softip/monitoramento_solar/solarmon/assets/uploads/plantas/52ae2-sistema-fotovoltaico-artigos-cursos-cpt.jpg

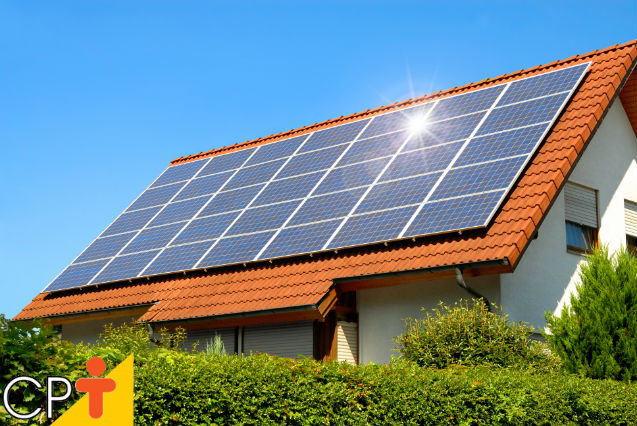
solarmon/assets/uploads/plantas/52ae2-sistema-fotovoltaico-artigos-cursos-cpt.jpg
