softip/monitoramento_solar/circuito.jpg

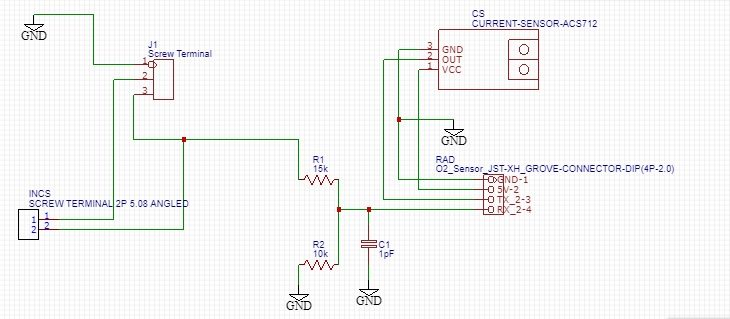
circuito.jpg
