softip/monitoramento_solar/fotos/09052019_1.jpg

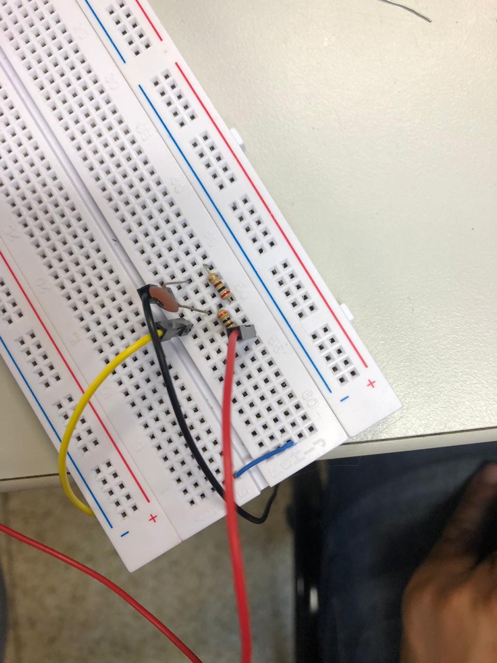
fotos/09052019_1.jpg
