softip/monitoramento_solar/fotos/09052019_2.jpg

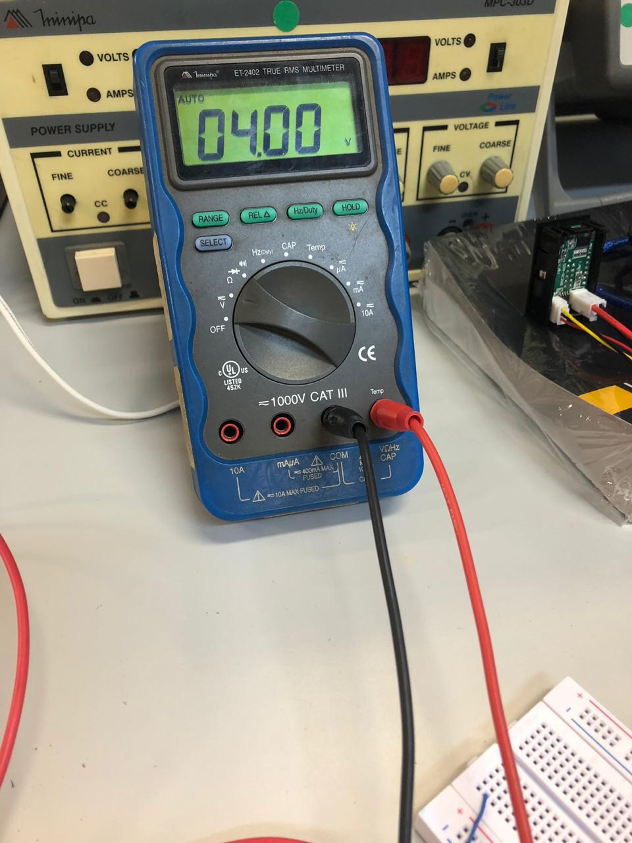
fotos/09052019_2.jpg
