softip/monitoramento_solar/fotos/09052019_3.jpg

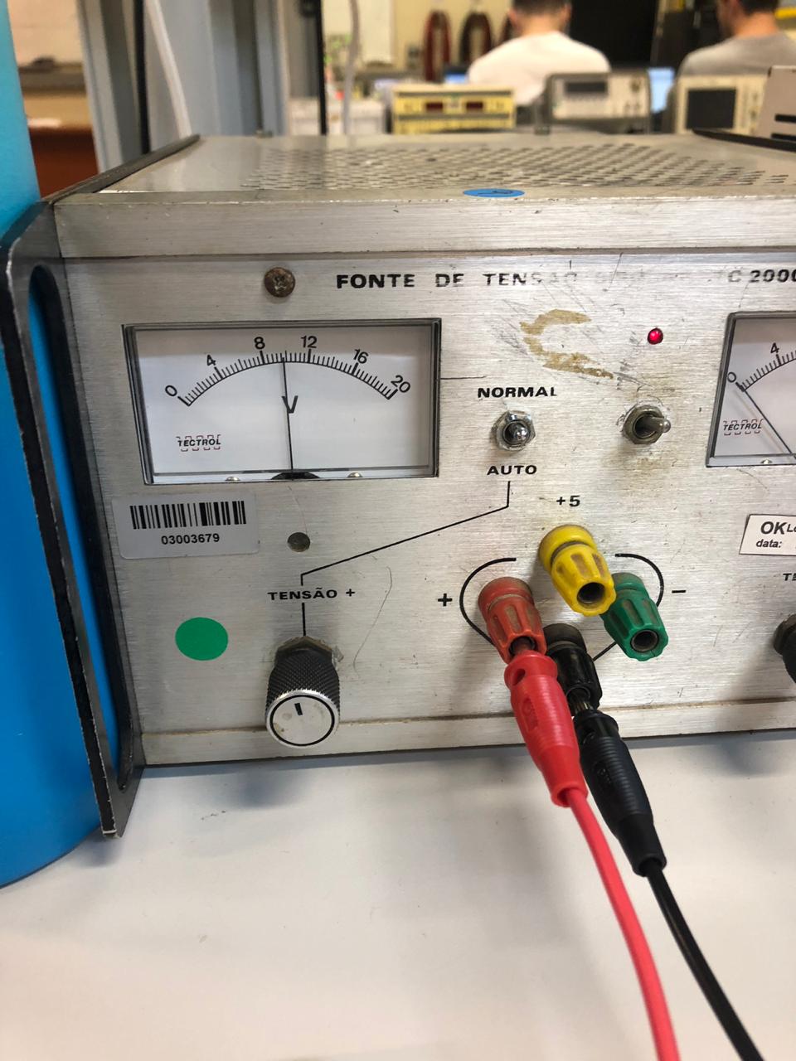
fotos/09052019_3.jpg
