softip/monitoramento_solar/fotos/09052019_4.jpg

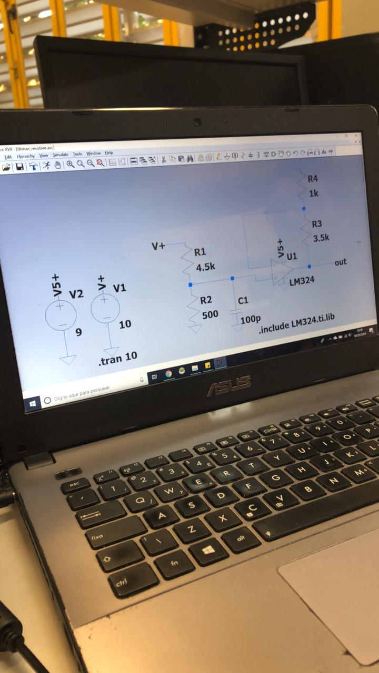
fotos/09052019_4.jpg
