softip/monitoramento_solar/fotos/09052019_5.jpg

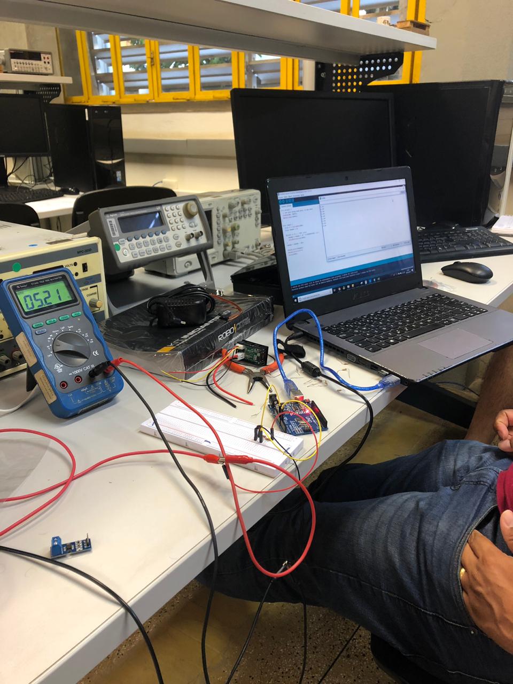
fotos/09052019_5.jpg
