softip/monitoramento_solar/fotos/09052019_6.jpg

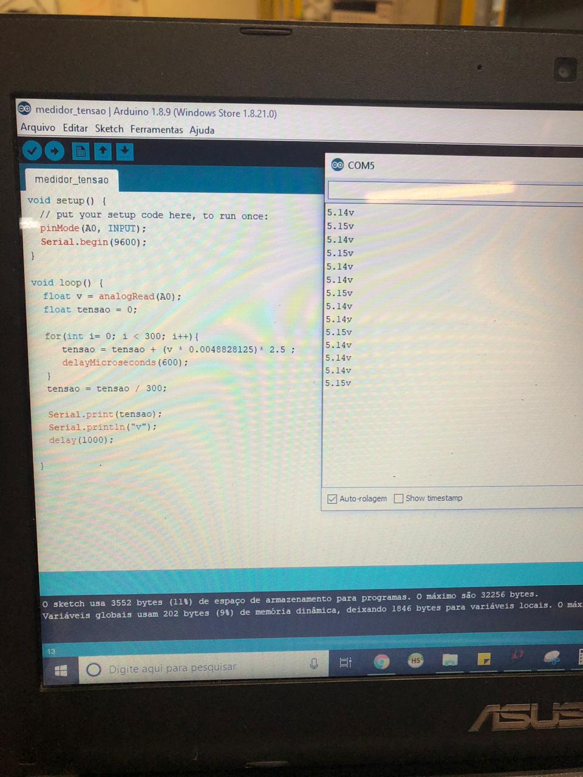
fotos/09052019_6.jpg
