softip/monitoramento_solar/fotos/25042919.jpg

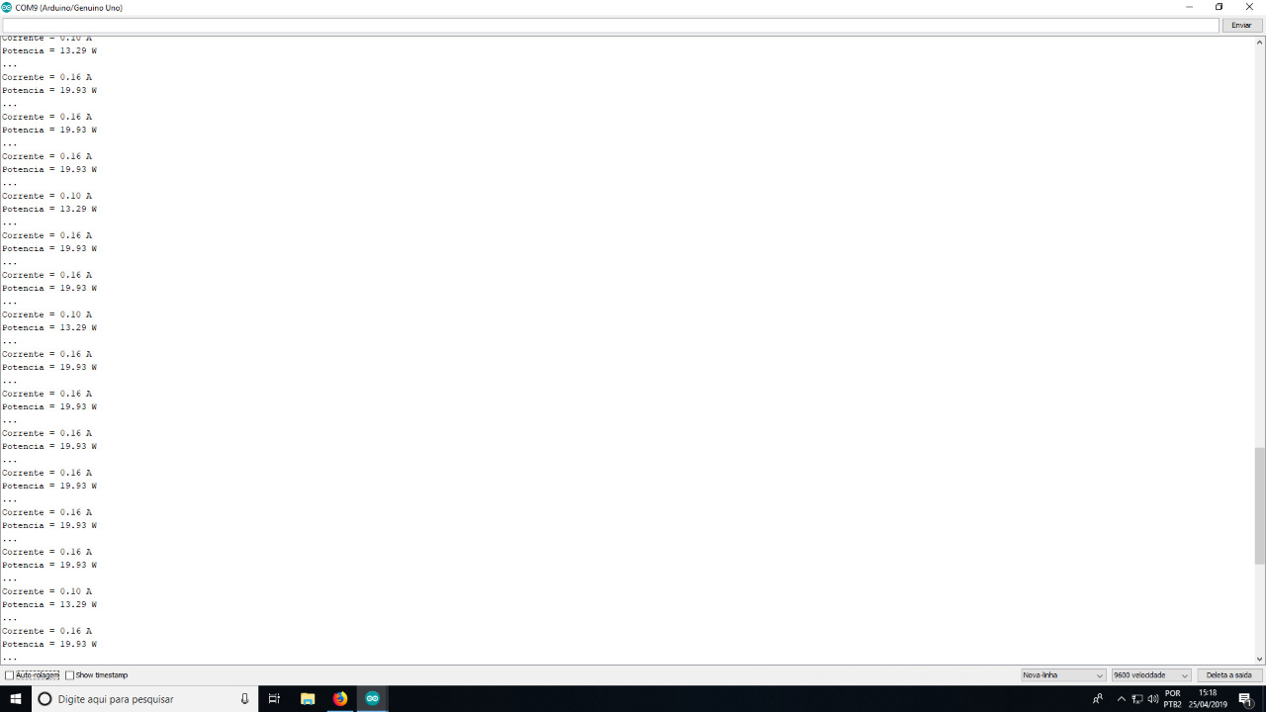
fotos/25042919.jpg
