softip/monitoramento_solar/fotos/divisor_resistivo.jpg

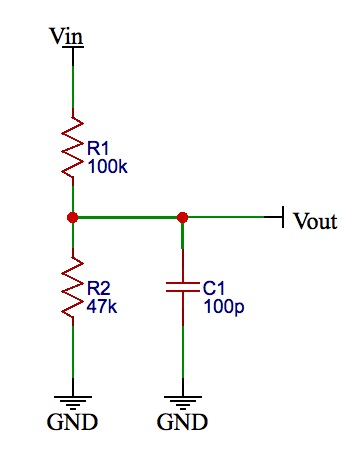
fotos/divisor_resistivo.jpg
