softip/monitoramento_solar/solarmon/assets/uploads/clientes/2666a-unicamp.png

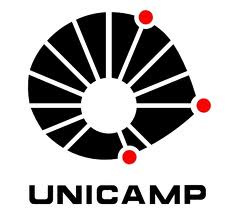
solarmon/assets/uploads/clientes/2666a-unicamp.png
