softip/monitoramento_solar/solarmon/assets/uploads/plantas/c3c21-untitled-1.jpg

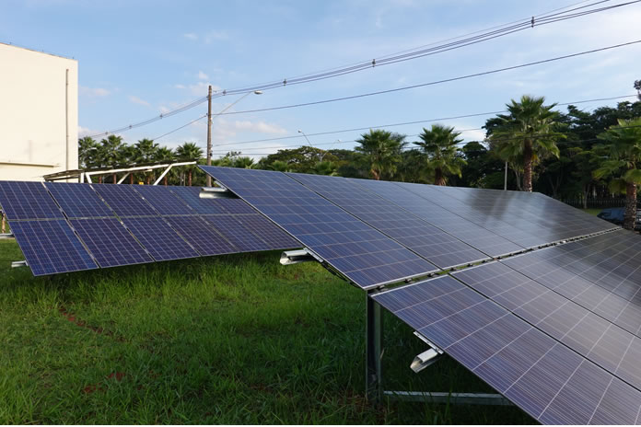
solarmon/assets/uploads/plantas/c3c21-untitled-1.jpg
