softip/monitoramento_solar/Sensor/Headers.h

// Header.h : cabecalhos de classes

// Mais informacoes em www.radiuino.cc
// Copyright (c) 2015
// Author: Pedro Henrique Gomes, Omar C. Branquinho, Tiago T. Ganselli e Debora M Ferreira, Guilherme Lopes da Silva, Raphael Montali de Assumpçao.
// Versao 2.3: 18/05/2017

// Este arquivo e parte da plataforma Radiuino
// Este programa e um software livre; voce pode redistribui-lo e/ou modifica-lo dentro dos termos da Licenca Publica Geral Menor GNU 
// como publicada pela Fundacao do Software Livre (FSF); na versao 2 da Licenca, ou (na sua opniao) qualquer futura versao.
// Este programa e distribuido na esperanca que possa ser  util, mas SEM NENHUMA GARANTIA; sem uma garantia implicita 
// de ADEQUACAO a qualquer MERCADO ou APLICACAO EM PARTICULAR. Veja a Licenca Publica Geral Menor GNU para maiores detalhes.
// Voce deve ter recebido uma copia da Licenca Publica Geral Menor GNU junto com este programa, se nao, escreva para a Fundacao 
// do Software Livre(FSF) Inc., 51 Franklin St, Fifth Floor, Boston, MA  02110-1301  USA
    
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
#ifndef HEADERS_H
#define HEADERS_H 1

/**
 * Estrutura do pacote a ser transmitido e recebido. O pacote possui 52 bytes, sendo 4 bytes de cabecalho de camada fisica (Phy), 4 bytes de cabecalho
 * de camada de Controle de Acesso ao Meio (MAC), 4 bytes de cabecalho de camada de Rede (Net), 4 bytes de cabecalho de camada de Transporte (Transp) e
 * e 4 bytes de cabecalho de camada de Aplicacao (App). Os 36 bytes restantes sao reservados para payload de AD e IO.
 */
typedef struct 
{  
  /* Cabecalho da camada Fisica (Phy) */
  byte PhyHdr[4];
  
  /* Cabecalho da camada de Controle de Acesso ao Meio (MAC) */
  byte MACHdr[4];
  
  /* Cabecalho da camada de Rede (Net) */
  byte NetHdr[4];
  
  /* Cabecalho da camada de Transporte (Transp) */
  byte TranspHdr[4];
  
  
  
  /* Bytes o payload de AD */
  byte AD0[3];
  byte AD1[3];
  byte AD2[3];
  byte AD3[3];
  byte AD4[3];
  byte AD5[3];  
  
  /* Bytes do payload de IO */
  byte IO0[3];
  byte IO1[3];
  byte IO2[3];
  byte IO3[3];
  byte IO4[3];
  byte IO5[3];  
  
} packet;

packet g_pkt;

/**
 * Classe de camada de Aplicacao
 */
 
#define AD0_PIN  0
#define AD1_PIN  1
#define AD2_PIN  2
#define AD3_PIN  3
#define AD4_PIN  4
#define AD5_PIN  5

#define IO0_PIN  4
#define IO1_PIN  5
#define IO2_PIN  6
#define IO3_PIN  7
#define IO4_PIN  8
#define IO5_PIN  9

class APP
{
  public:
    APP(void);
    inline void initialize(void);
    inline void send(packet * pkt);
    inline void receive(packet * pkt);

  private:
    int IO_0, IO_1, IO_2, IO_3, IO_4, IO_5;

};

/* Objeto de acesso a classe da camada de Aplicacao */
extern APP App;

/**
 * Classe de camada de Transporte
 */
class TRANSP
{
  public:
    TRANSP(void);
    inline void initialize(void);
    inline void send(packet * pkt);
    inline void receive(packet * pkt);

  private:
  
};

/* Objeto de acesso a classe da camada de Transporte */
extern TRANSP Transp;

/**
 * Classe de camada de Rede
 */
class NET
{
  public:
    NET(void);
    inline void initialize(void);
    inline void send(packet * pkt);
    inline void receive(packet * pkt);
    void swapAddresses(packet * pkt);
    
    byte my_addr;
  private:
    
};

/* Objeto de acesso a classe da camada de Rede */
extern NET Net;

/**
 * Classe de camada de Controle de Acesso ao Meio
 */
#define  SLEEP_MSG  1
#define  SLEEP_ACK  2
#define  SLEEP2_MSG  3
#define  SLEEP2_ACK  4

class MAC
{
  public:
    MAC(void);
    inline void initialize(void);
    inline void send(packet * pkt);
    inline void receive(packet * pkt);
    
    volatile int time_to_sleep;
    /* variaveis para o sleep2 */
    volatile unsigned long t2;
    volatile int t3;
    volatile boolean flag_sleep2;
    volatile unsigned long last_wakeup;
  private:
    
};

/* Objeto de acesso a classe da camada de Controle de Acesso ao Meio */
extern MAC Mac;

/**
 * Classe de camada Fisica
 */
#define BUFFLEN1  CC1101_PACKT_LEN
byte serialData[BUFFLEN1 + 1];

class PHY
{
  public:
    PHY(void);
    inline void initialize();
    inline void send(packet * pkt);
    inline int receive(packet * pkt);
    
    void sendSerial(packet * pkt);
    void receiveSerial(void);
    
    byte txFifoFree(void);
    void setChannel(byte channel);
    void lowPowerOn(void);    
    void setPower(byte power);
    void setFreqOffset(byte freq_offset);
    void setRadio(int set_radio);
    
    boolean carrierSense(void);
    
    byte power;                 /* Potencia */
    byte channel;               /* Canal */
    byte freq_offset;           /* Offset de frequencia */
    int serial_baudrate;        /* Serial baudrate */
    int set_radio;        /* Ajusta o tipo de rádio */
    
    //incremento do pisca do led
    int RxLedBlink;
    int TxLedBlink;
  
  private:
    int initCC1101Config(void);
    void configWatchdog(int time);
    void strobe_idle_wait(void);
};

/* Objeto de acesso a classe da camada Fisica */
extern PHY Phy;

/* Configuracao de registradores do CC1101. Obtidos atraves do SmartRF Studio 7 */
// Deviation = 4.760742 
// Base frequency = 914.999969 
// Carrier frequency = 914.999969 
// Channel number = 0 
// Carrier frequency = 914.999969 
// Modulated = true 
// Modulation format = 2-FSK 
// Manchester enable = false 
// Sync word qualifier mode = 30/32 sync word bits detected 
// Preamble count = 4 
// Channel spacing = 124.969482
// Carrier frequency = 914.999969 
// Data rate = 9.59587 
// RX filter BW = 203.125000 
// Data format = Normal mode 
// CRC enable = true 
// Device address = 0 
// Address config = No address check 
// CRC autoflush = false 
// PA ramping = false 
// TX power = 10

const byte CC1101_registerSettings[CC1101_NR_OF_CONFIGS][CC1101_NR_OF_REGISTERS] PROGMEM = {
{ 
    0x04,  // IOCFG2        GDO2 Output Pin Configuration
    0x07,  // IOCFG0        GDO0 Output Pin Configuration
    0x07,  // FIFOTHR       RX FIFO and TX FIFO Thresholds
    0x34,  // PKTLEN        Packet Length
    0x04,  // PKTCTRL1      Packet Automation Control
    0x04,  // PKTCTRL0      Packet Automation Control
    0x00,  // ADDR          Device Address
    0x00,  // CHANNR        Channel Number
    0x06,  // FSCTRL1       Frequency Synthesizer Control
    0x00,  // FSCTRL0       Frequency Synthesizer Control
    0x23,  // FREQ2         Frequency Control Word, High Byte
    0x31,  // FREQ1         Frequency Control Word, Middle Byte
    0x3B,  // FREQ0         Frequency Control Word, Low Byte
    0x4A,  // MDMCFG4       Modem Configuration
    0x83,  // MDMCFG3       Modem Configuration
    0x03,  // MDMCFG2       Modem Configuration
    0x22,  // MDMCFG1       Modem Configuration
    0x3B,  // MDMCFG0       Modem Configuration
    0x60,  // DEVIATN       Modem Deviation Setting
    0x18,  // MCSM0         Main Radio Control State Machine Configuration
    0x16,  // FOCCFG        Frequency Offset Compensation Configuration
    0x1C,  // BSCFG         Bit Synchronization Configuration
    0x7B,  // AGCCTRL2      AGC Control
    0x00,  // AGCCTRL1      AGC Control
    0xB0,  // AGCCTRL0      AGC Control
    0xB6,  // FREND1        Front End RX Configuration
    0x10,  // FREND0        Front End TX Configuration
    0xE9,  // FSCAL3        Frequency Synthesizer Calibration
    0x2A,  // FSCAL2        Frequency Synthesizer Calibration
    0x00,  // FSCAL1        Frequency Synthesizer Calibration
    0x1F,  // FSCAL0        Frequency Synthesizer Calibration
    0x59,  // FSTEST        Frequency Synthesizer Calibration Control
    0x88,  // TEST2         Various Test Settings
    0x31,  // TEST1         Various Test Settings
    0x09,  // TEST0         Various Test Settings 
}
};

const byte CC1101_paTable[CC1101_NR_OF_CONFIGS][CC1101_PA_TABLESIZE] PROGMEM ={
// -30  -20   -15  -10    0   5    7   10
  {0x03,0x0E,0x1E,0x27,0x8E,0x84,0xCC,0xC3},    // Configuracao 0
};

#endif
