softip/monitoramento_solar/bibliotecas sensor/Radiuino/TimerOne.cpp

/*
 *  Interrupt and PWM utilities for 16 bit Timer1 on ATmega168/328
 *  Original code by Jesse Tane for http://labs.ideo.com August 2008
 *  Modified March 2009 by Jérôme Despatis and Jesse Tane for ATmega328 support
 *  Modified June 2009 by Michael Polli and Jesse Tane to fix a bug in setPeriod() which caused the timer to stop
 *  Modified June 2011 by Lex Talionis to add a function to read the timer
 *
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
 *  See Google Code project http://code.google.com/p/arduino-timerone/ for latest
 */

#include "RADIUINO.h"

TimerOne Timer1;              // preinstatiate

ISR(TIMER1_OVF_vect)          // interrupt service routine that wraps a user defined function supplied by attachInterrupt
{
  Timer1.isrCallback();
}

void TimerOne::initialize(long microseconds)
{
  TCCR1A = 0;                 // clear control register A 
  TCCR1B = _BV(WGM13);        // set mode 8: phase and frequency correct pwm, stop the timer
  setPeriod(microseconds);
}

void TimerOne::setPeriod(long microseconds)
{
  long cycles = (F_CPU / 2000000) * microseconds;                                // the counter runs backwards after TOP, interrupt is at BOTTOM so divide microseconds by 2
  if(cycles < RESOLUTION)              clockSelectBits = _BV(CS10);              // no prescale, full xtal
  else if((cycles >>= 3) < RESOLUTION) clockSelectBits = _BV(CS11);              // prescale by /8
  else if((cycles >>= 3) < RESOLUTION) clockSelectBits = _BV(CS11) | _BV(CS10);  // prescale by /64
  else if((cycles >>= 2) < RESOLUTION) clockSelectBits = _BV(CS12);              // prescale by /256
  else if((cycles >>= 2) < RESOLUTION) clockSelectBits = _BV(CS12) | _BV(CS10);  // prescale by /1024
  else        cycles = RESOLUTION - 1, clockSelectBits = _BV(CS12) | _BV(CS10);  // request was out of bounds, set as maximum
  ICR1 = pwmPeriod = cycles;                                                     // ICR1 is TOP in p & f correct pwm mode
  TCCR1B &= ~(_BV(CS10) | _BV(CS11) | _BV(CS12));
  TCCR1B |= clockSelectBits;                                                     // reset clock select register
}

void TimerOne::setPwmDuty(char pin, int duty)
{
  unsigned long dutyCycle = pwmPeriod;
  dutyCycle *= duty;
  dutyCycle >>= 10;
  if(pin == 1 || pin == 9)       OCR1A = dutyCycle;
  else if(pin == 2 || pin == 10) OCR1B = dutyCycle;
}

void TimerOne::pwm(char pin, int duty, long microseconds)  // expects duty cycle to be 10 bit (1024)
{
  if(microseconds > 0) setPeriod(microseconds);
  if(pin == 1 || pin == 9) {
    DDRB |= _BV(PORTB1);                                   // sets data direction register for pwm output pin
    TCCR1A |= _BV(COM1A1);                                 // activates the output pin
  }
  else if(pin == 2 || pin == 10) {
    DDRB |= _BV(PORTB2);
    TCCR1A |= _BV(COM1B1);
  }
  setPwmDuty(pin, duty);
  start();
}

void TimerOne::disablePwm(char pin)
{
  if(pin == 1 || pin == 9)       TCCR1A &= ~_BV(COM1A1);   // clear the bit that enables pwm on PB1
  else if(pin == 2 || pin == 10) TCCR1A &= ~_BV(COM1B1);   // clear the bit that enables pwm on PB2
}

void TimerOne::attachInterrupt(void (*isr)(), long microseconds)
{
  if(microseconds > 0) setPeriod(microseconds);
  isrCallback = isr;                                       // register the user's callback with the real ISR
  TIMSK1 = _BV(TOIE1);                                     // sets the timer overflow interrupt enable bit
  sei();                                                   // ensures that interrupts are globally enabled
  start();
}

void TimerOne::detachInterrupt()
{
  TIMSK1 &= ~_BV(TOIE1);                                   // clears the timer overflow interrupt enable bit 
}

void TimerOne::start()
{
  TCCR1B |= clockSelectBits;
}

void TimerOne::stop()
{
  TCCR1B &= ~(_BV(CS10) | _BV(CS11) | _BV(CS12));          // clears all clock selects bits
}

void TimerOne::restart()
{
  TCNT1 = 0;
}

unsigned long TimerOne::read()		//returns the value of the timer in microseconds
{									//rember! phase and freq correct mode counts up to then down again
	unsigned int tmp=TCNT1;
	char scale=0;
	switch (clockSelectBits)
	{
	case 1:// no prescalse
		scale=0;
		break;
	case 2:// x8 prescale
		scale=3;
		break;
	case 3:// x64
		scale=6;
		break;
	case 4:// x256
		scale=8;
		break;
	case 5:// x1024
		scale=10;
		break;
	}
	while (TCNT1==tmp) //if the timer has not ticked yet
	{
		//do nothing -- max delay here is ~1023 cycles
	}
	tmp = (  (TCNT1>tmp) ? (tmp) : (ICR1-TCNT1)+ICR1  );//if we are counting down add the top value to how far we have counted down
	return ((tmp*1000L)/(F_CPU /1000L))<<scale;
}
